sarnau/HP-8711C-RF-Network-Analyzer/datasheets/s-l1600-4.jpg

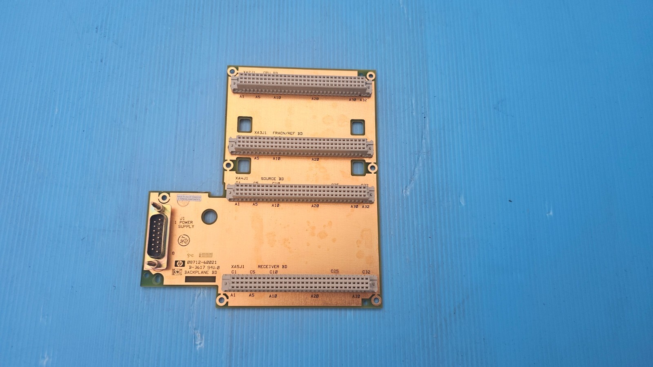
datasheets/s-l1600-4.jpg
