sarnau/HP-8711C-RF-Network-Analyzer/HP 08712-60012 Service Kit Photos/8711-8712-8713-8714-service-kit-image-No-1.jpg

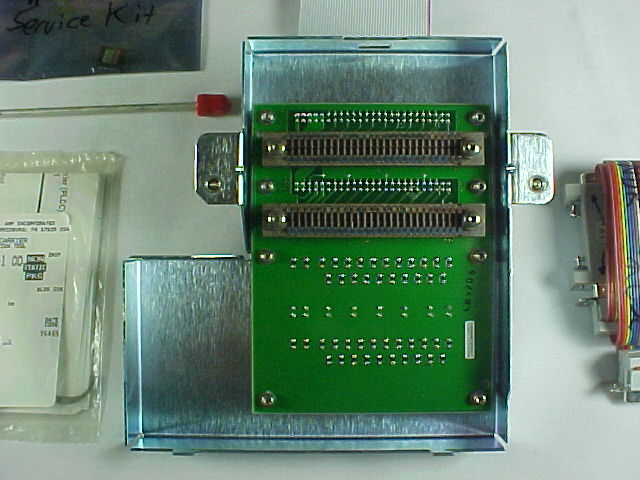
HP 08712-60012 Service Kit Photos/8711-8712-8713-8714-service-kit-image-No-1.jpg
