sarnau/HP-8711C-RF-Network-Analyzer/LCD-upgrade/LCD_masking_the_frame.jpg

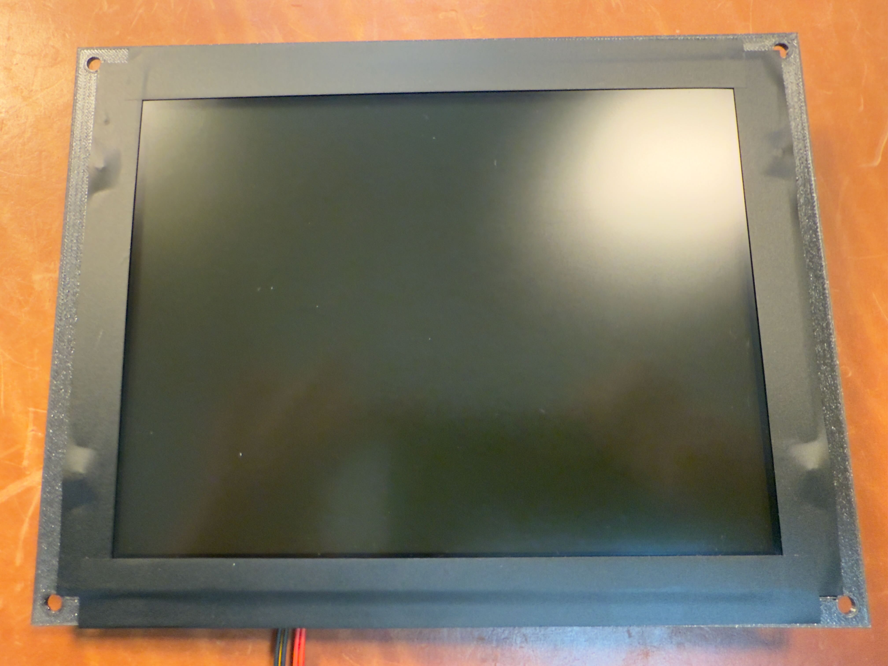
LCD-upgrade/LCD_masking_the_frame.jpg
