sarnau/HP-8711C-RF-Network-Analyzer/LCD-upgrade/LCD_mounting_VGA.jpg

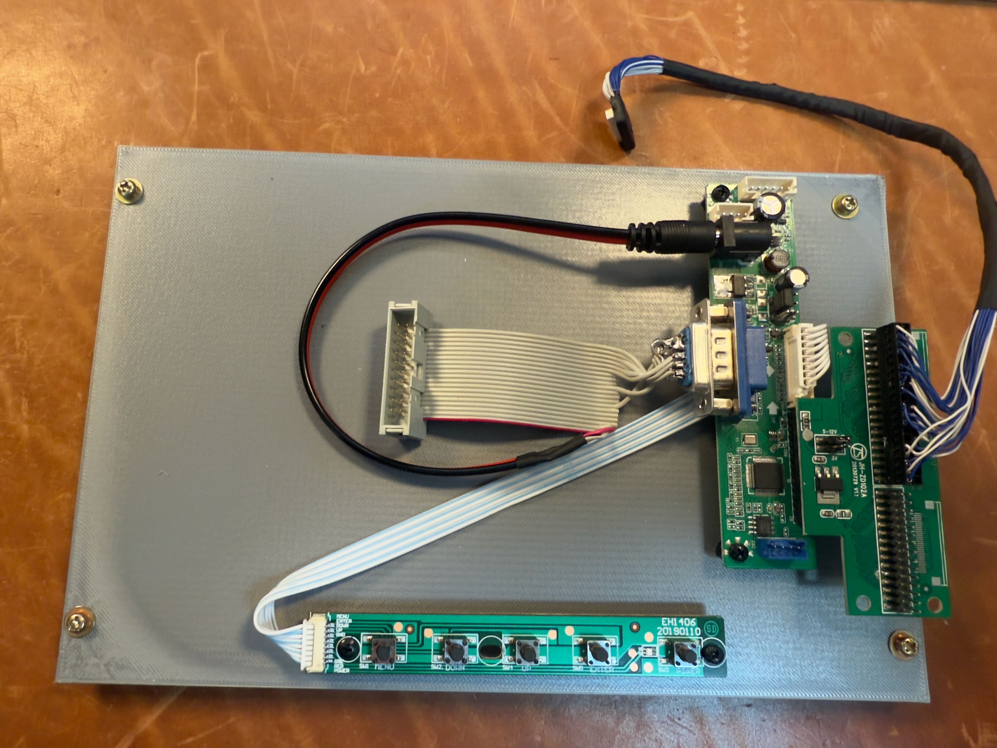
LCD-upgrade/LCD_mounting_VGA.jpg
